duffwv/LayerFused-X301-Mods/blind-joint/base-sliding-tnut-spacers/spacers/img/spacers-side-org.jpeg

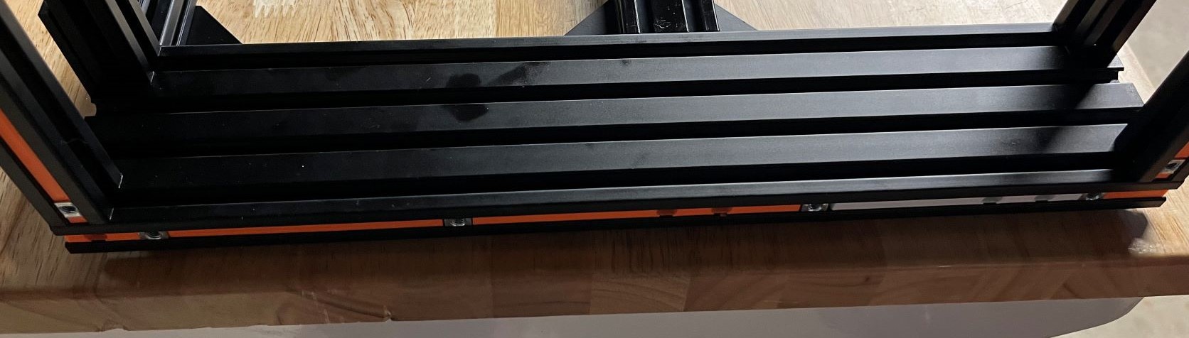
blind-joint/base-sliding-tnut-spacers/spacers/img/spacers-side-org.jpeg
