duffwv/LayerFused-X301-Mods/eva/diameter-17.7mm.png

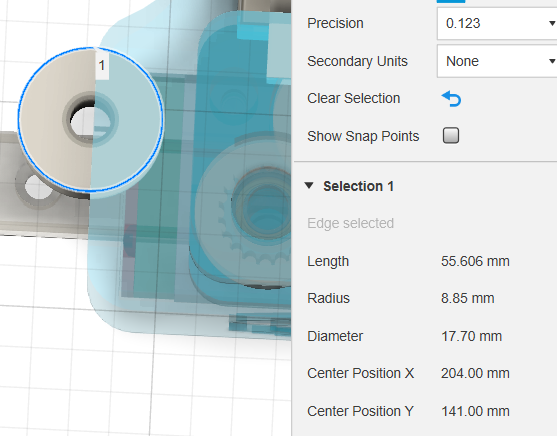
eva/diameter-17.7mm.png
