duffwv/LayerFused-X301-Mods/eva/from-right-front-12mm-drop.png

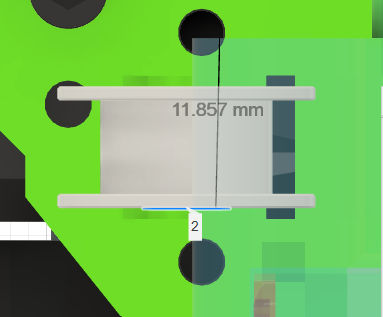
eva/from-right-front-12mm-drop.png
