duffwv/LayerFused-X301-Mods/MGN12C/XY Bracket Bottoms V2 Left.stl

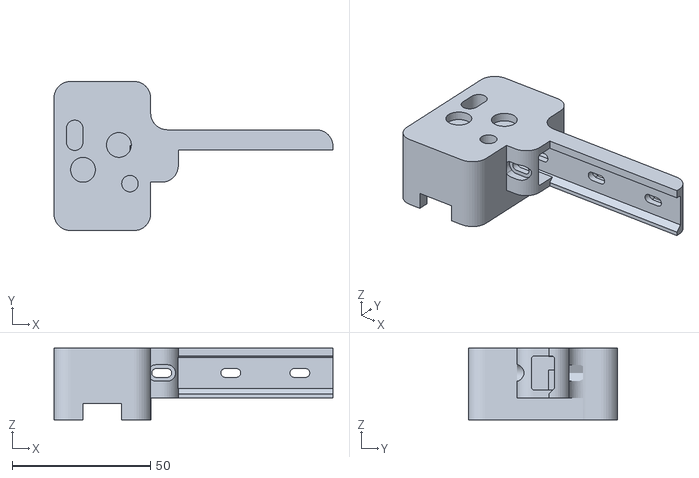
[picture p47: CAD file, 2023-02-08]
MGN12C/XY Bracket Bottoms V2 Left.stl
101.0 x 54.0 x 26.0
