duffwv/LayerFused-X301-Mods/sensorless-homing/y-homing-stops v2.stl

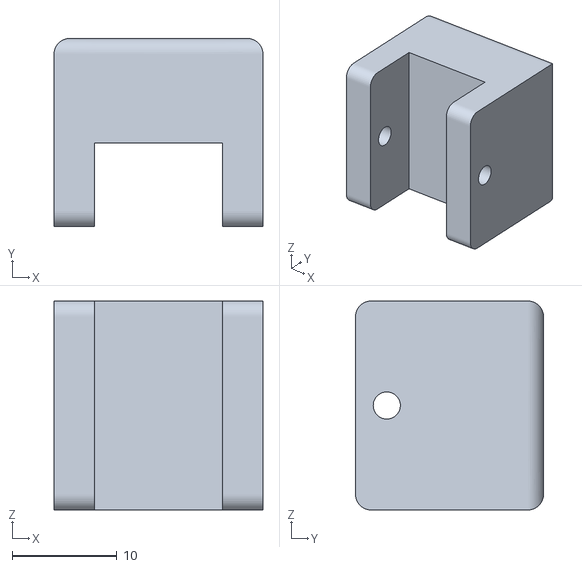
[picture p48: CAD file, 2023-02-08]
sensorless-homing/y-homing-stops v2.stl
20.0 x 18.0 x 20.0
