duffwv/LayerFused-X301-Mods/webcam-mount/stl/webcam-mount-plate-right.stl

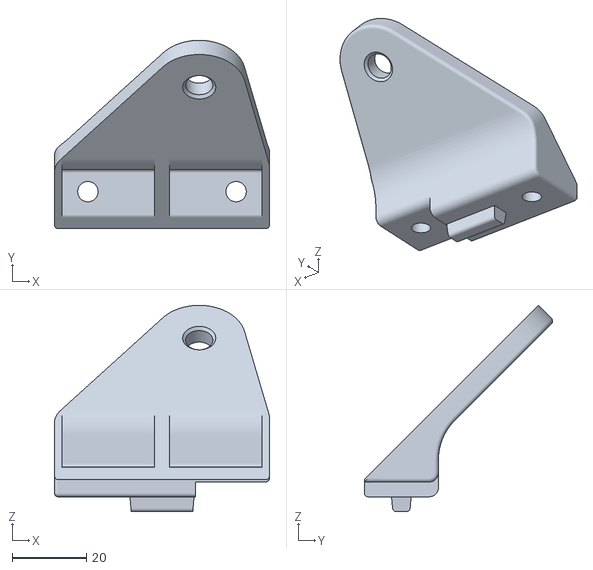
[picture p49: CAD file, 2023-02-08]
webcam-mount/stl/webcam-mount-plate-right.stl
58.0 x 50.8 x 55.7
