duffwv/LayerFused-X301-Mods/bed-leveling/bed-leveling-column-shim-1mm.stl

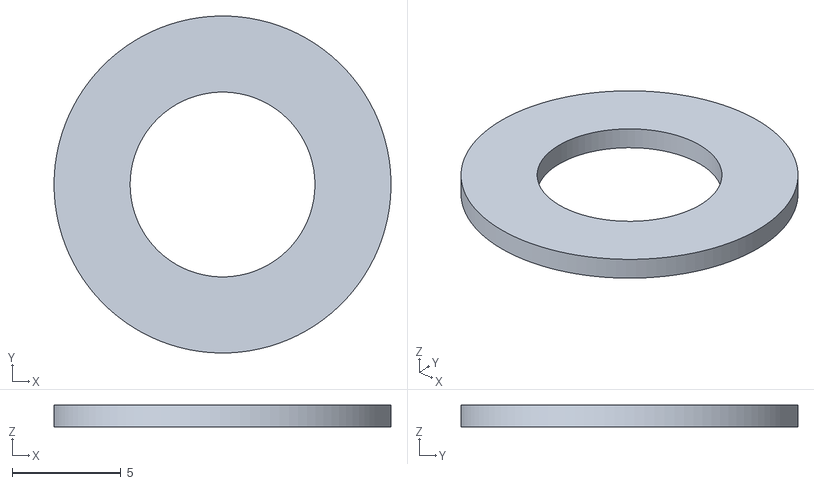
[picture p50: CAD file, 2023-02-08]
bed-leveling/bed-leveling-column-shim-1mm.stl
15.5 x 15.5 x 1.00
