duffwv/LayerFused-X301-Mods/blind-joint/base-sliding-tnut-spacers/spacers/STL/frontandback440mm/base-spacer-4mm.stl

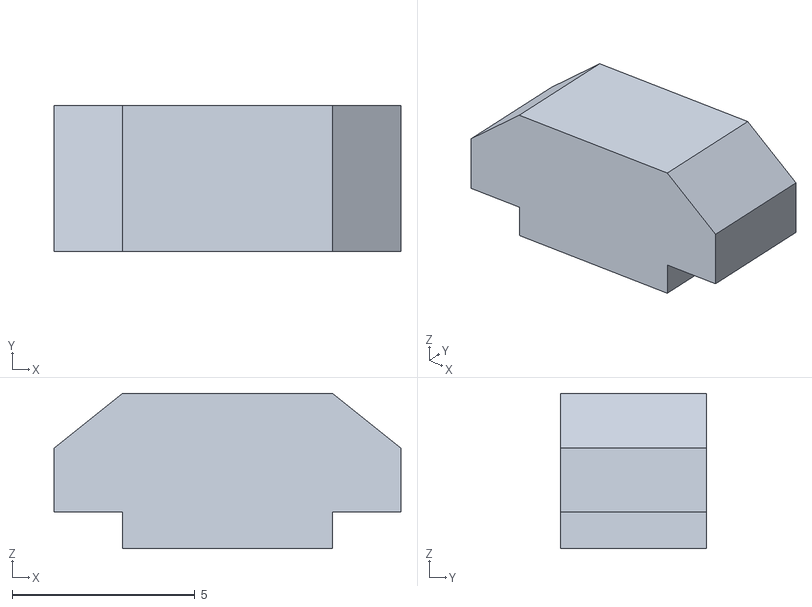
[picture p51: CAD file, 2023-02-08]
blind-joint/base-sliding-tnut-spacers/spacers/STL/frontandback440mm/base-spacer-4mm.stl
9.50 x 4.00 x 4.25
