duffwv/LayerFused-X301-Mods/blind-joint/base-sliding-tnut-spacers/spacers/STL/side400mm/base-spacer-119mm-slot29-slot49.stl

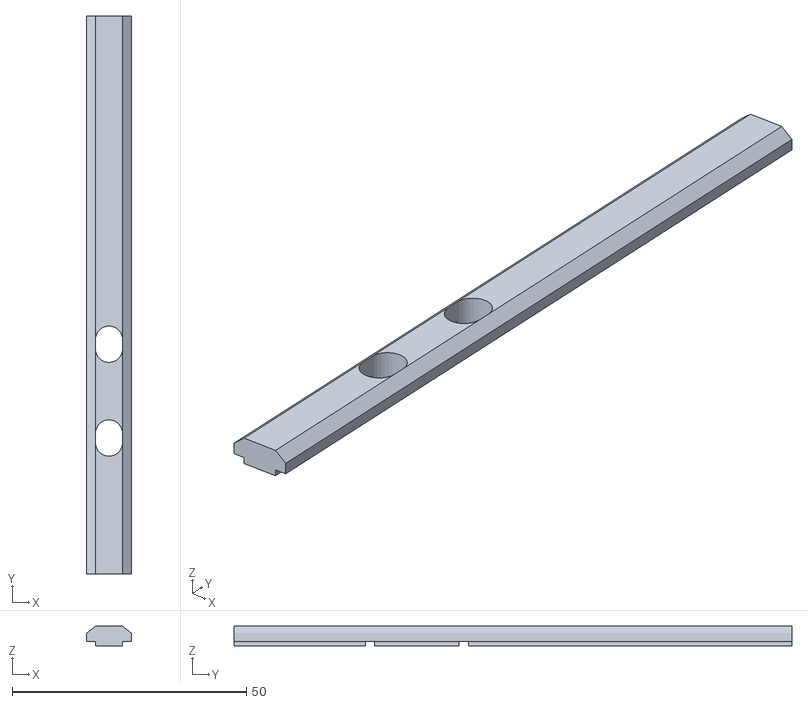
[picture p52: CAD file, 2023-02-08]
blind-joint/base-sliding-tnut-spacers/spacers/STL/side400mm/base-spacer-119mm-slot29-slot49.stl
9.50 x 119.0 x 4.25
