duffwv/LayerFused-X301-Mods/blind-joint/spacing_guides/extrusion-channel-center-punch-guides/blind-joint-drill-guide-10mm-and-3z v3.stl

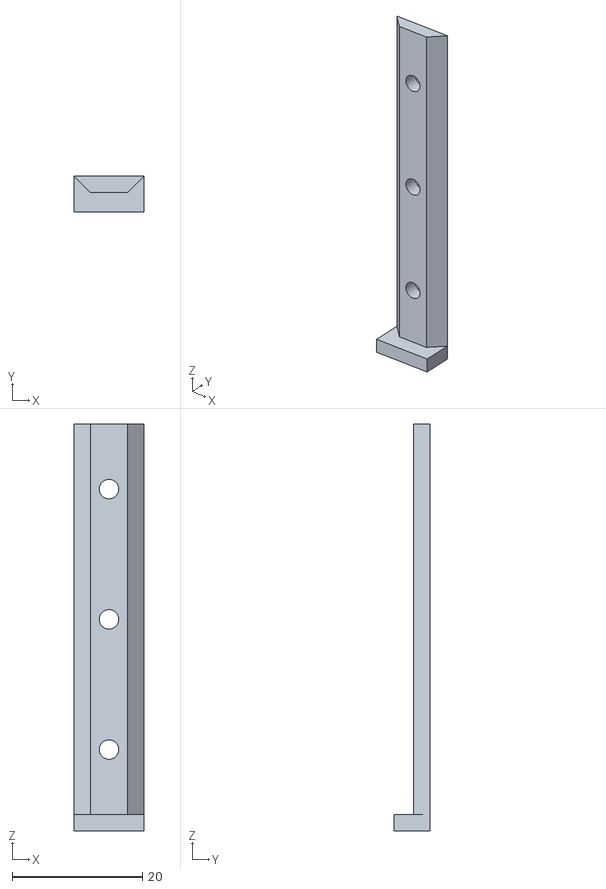
[picture p53: CAD file, 2023-02-08]
blind-joint/spacing_guides/extrusion-channel-center-punch-guides/blind-joint-drill-guide-10mm-and-3z v3.stl
10.8 x 5.50 x 62.5
