duffwv/LayerFused-X301-Mods/btt-tft35-spi-display-mount/TFT35 SPI Display Case - LayerFused X301.stl

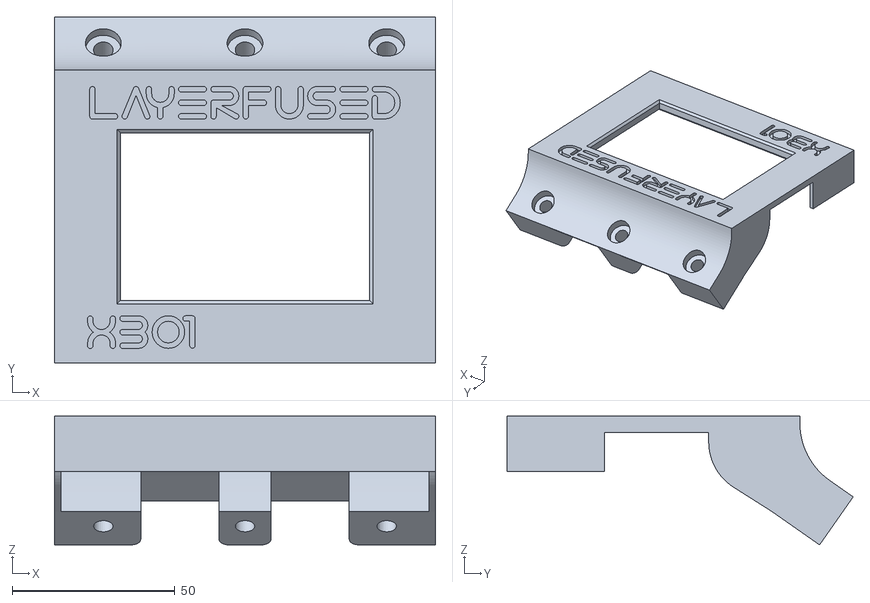
[picture p54: CAD file, 2023-02-08]
btt-tft35-spi-display-mount/TFT35 SPI Display Case - LayerFused X301.stl
117.0 x 106.4 x 39.6
