duffwv/LayerFused-X301-Mods/cover/1mm-pinch/cover-edges-straight-149.stl

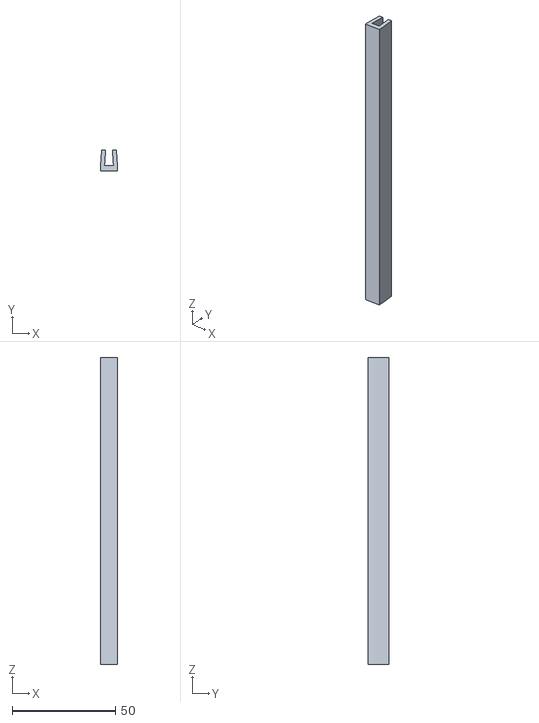
[picture p55: CAD file, 2023-02-08]
cover/1mm-pinch/cover-edges-straight-149.stl
8.25 x 10.0 x 149.0
