duffwv/LayerFused-X301-Mods/MGN12C/Z Carriage Bracket.stl

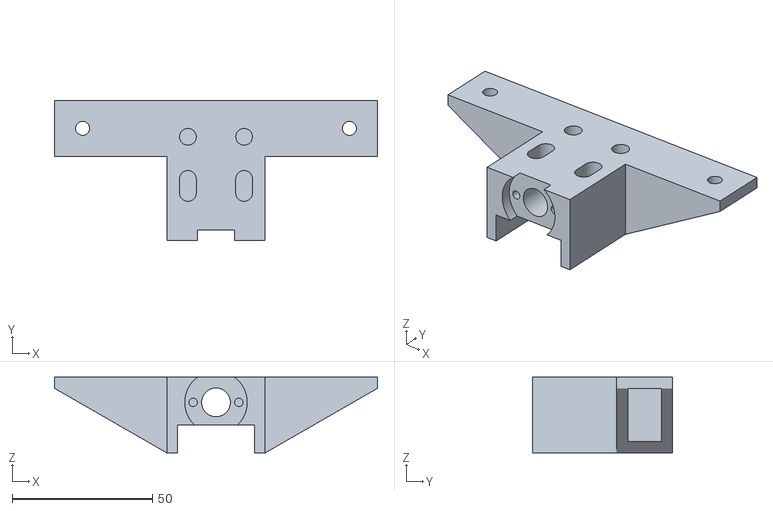
[picture p56: CAD file, 2023-02-08]
MGN12C/Z Carriage Bracket.stl
115.0 x 50.0 x 27.0
