duffwv/LayerFused-X301-Mods/webcam-mount/stl/webcam-mount-flush.stl

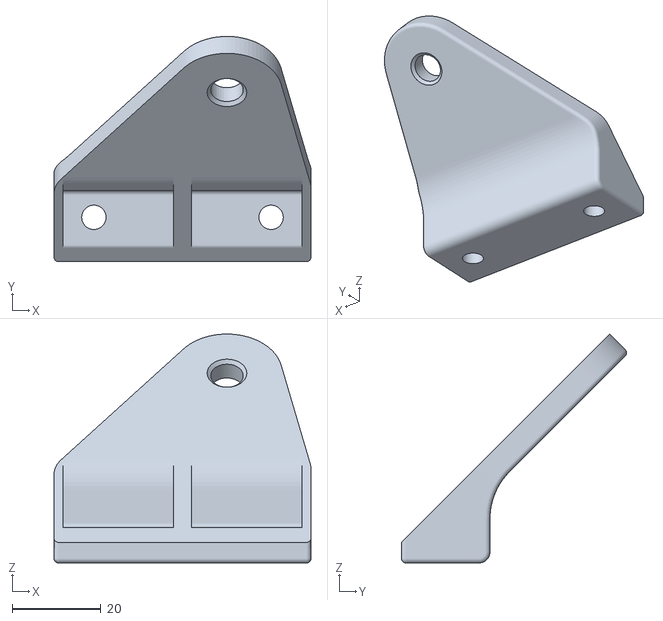
[picture p57: CAD file, 2023-02-08]
webcam-mount/stl/webcam-mount-flush.stl
58.0 x 50.8 x 51.7
