duffwv/LayerFused-X301-Mods/blind-joint/base-sliding-tnut-spacers/spacers/STL/frontandback440mm/base-spacer-front-back-104.stl

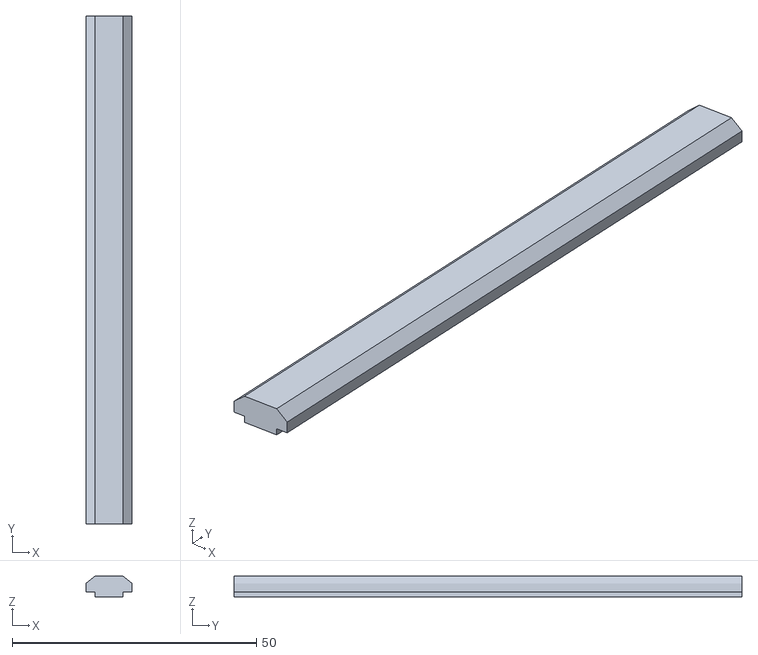
[picture p58: CAD file, 2023-02-08]
blind-joint/base-sliding-tnut-spacers/spacers/STL/frontandback440mm/base-spacer-front-back-104.stl
9.50 x 104.0 x 4.25
