duffwv/LayerFused-X301-Mods/blind-joint/base-sliding-tnut-spacers/spacers/STL/side400mm/base-spacer-94mm.stl

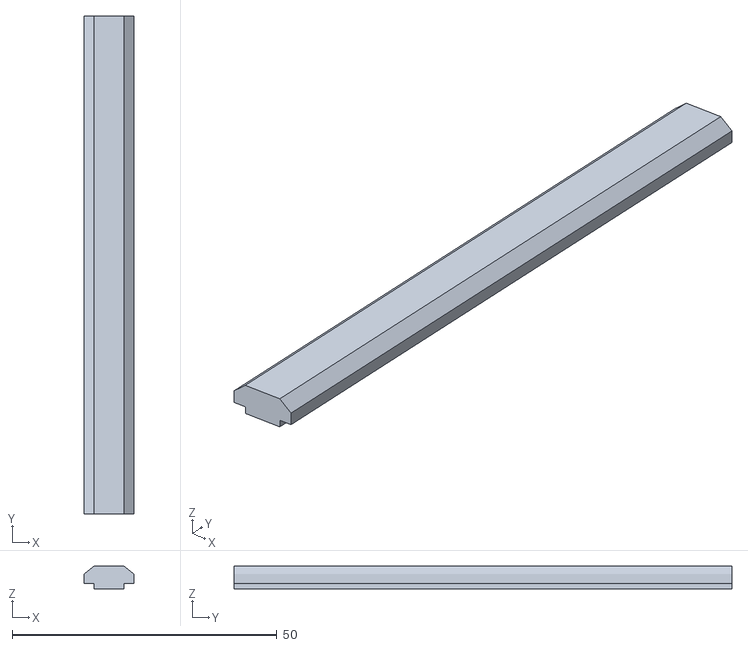
[picture p59: CAD file, 2023-02-08]
blind-joint/base-sliding-tnut-spacers/spacers/STL/side400mm/base-spacer-94mm.stl
9.50 x 94.0 x 4.25
