duffwv/LayerFused-X301-Mods/cover/1mm-pinch/cover-edges-corner-10mm.stl

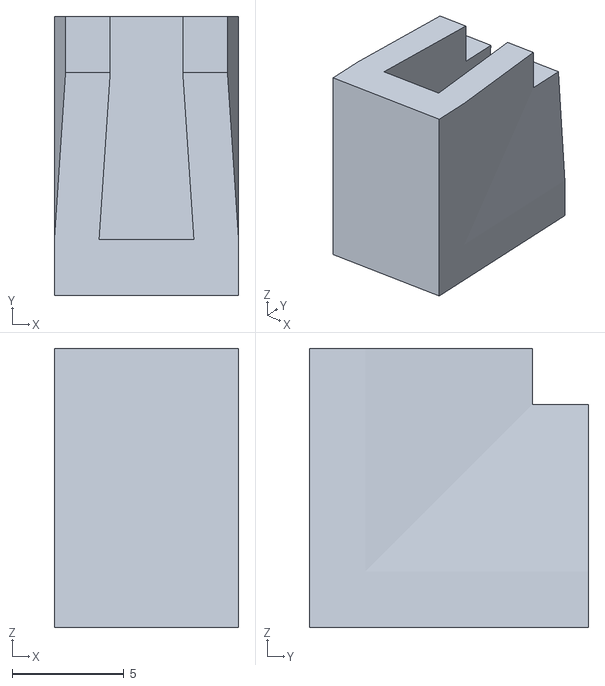
[picture p60: CAD file, 2023-02-08]
cover/1mm-pinch/cover-edges-corner-10mm.stl
8.25 x 12.5 x 12.5
