duffwv/LayerFused-X301-Mods/electronics-enclosure/board-mounts/mb8.stl

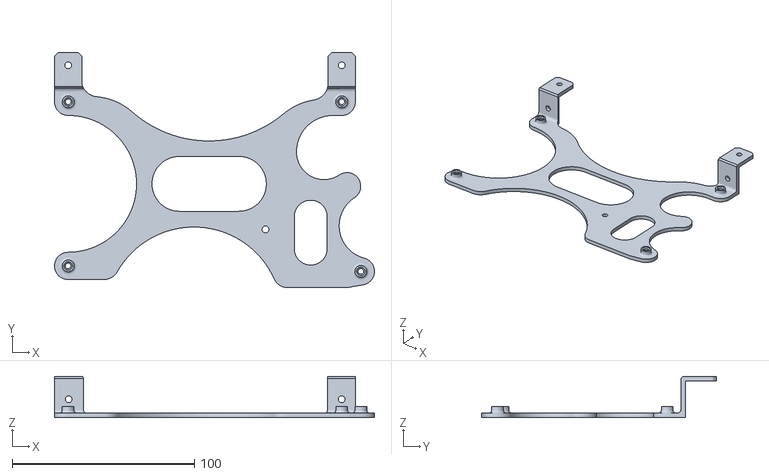
[picture p61: CAD file, 2023-02-08]
electronics-enclosure/board-mounts/mb8.stl
175.5 x 128.8 x 22.5
