duffwv/LayerFused-X301-Mods/bed-leveling/bed-leveling-column-shim-2mm.stl

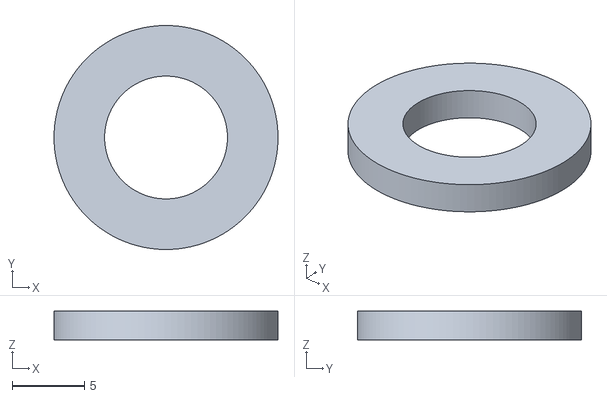
[picture p63: CAD file, 2023-02-08]
bed-leveling/bed-leveling-column-shim-2mm.stl
15.5 x 15.5 x 2.00
