duffwv/LayerFused-X301-Mods/cover/1mm-pinch/cover-edges-corner-47.5mm-27.5mm.stl

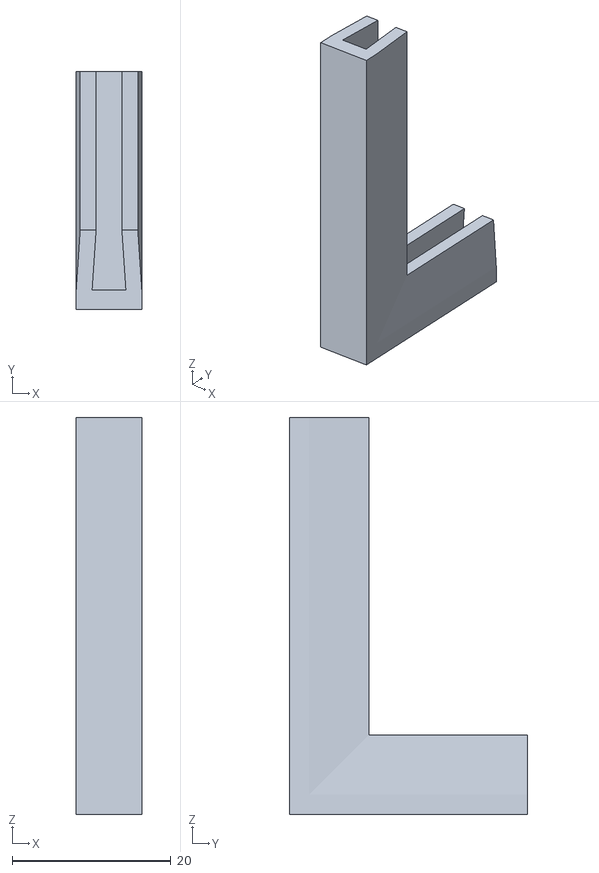
[picture p64: CAD file, 2023-02-08]
cover/1mm-pinch/cover-edges-corner-47.5mm-27.5mm.stl
8.25 x 30.0 x 50.0
