duffwv/LayerFused-X301-Mods/blind-joint/base-sliding-tnut-spacers/spacers/STL/side400mm/base-spacer-24mm.stl

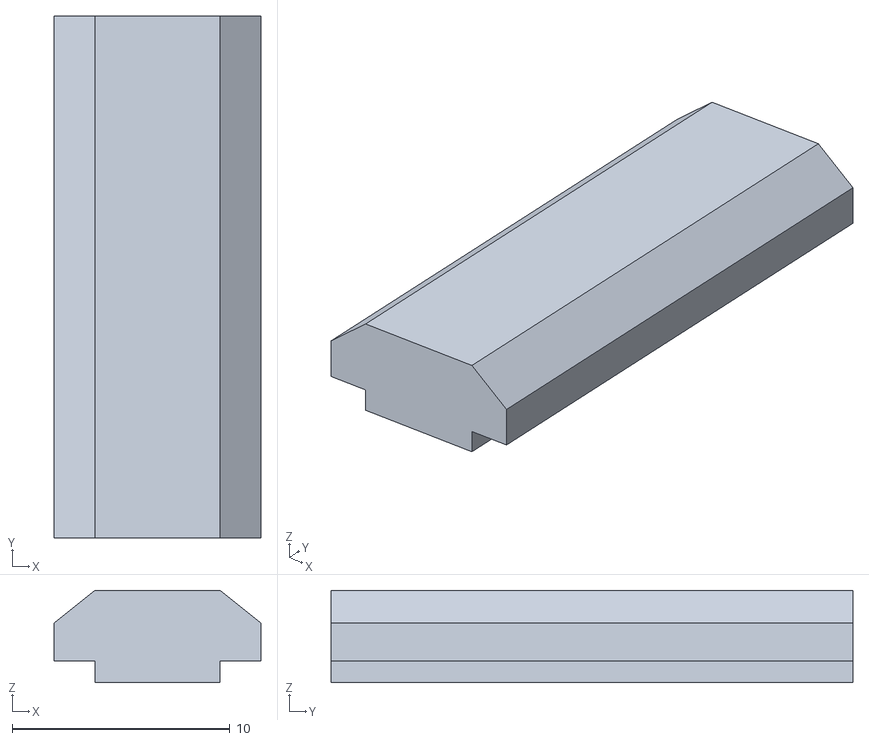
[picture p66: CAD file, 2023-02-08]
blind-joint/base-sliding-tnut-spacers/spacers/STL/side400mm/base-spacer-24mm.stl
9.50 x 24.0 x 4.25
