duffwv/LayerFused-X301-Mods/cover/1mm-pinch/cover-edges-straight-89.stl

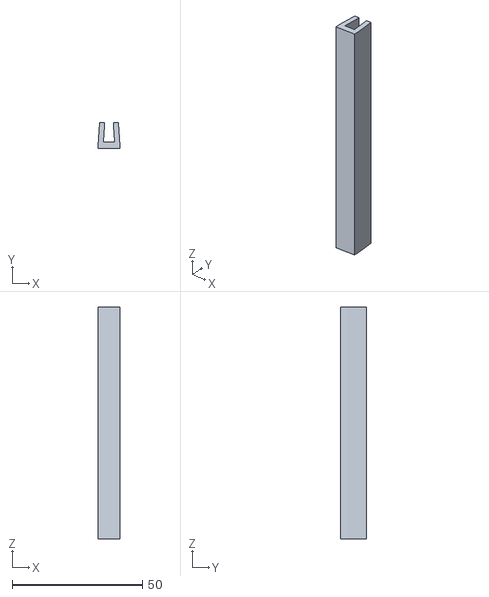
[picture p67: CAD file, 2023-02-08]
cover/1mm-pinch/cover-edges-straight-89.stl
8.25 x 10.0 x 89.0
