duffwv/LayerFused-X301-Mods/cover/1mm-pinch/cover-edges-testfit.stl

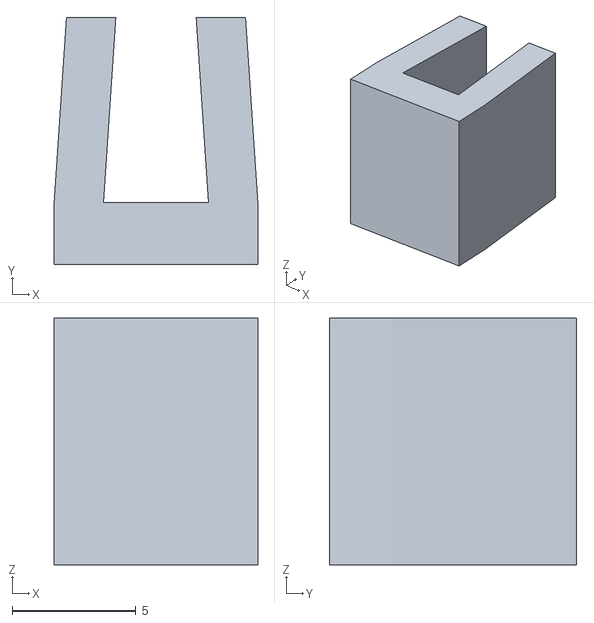
[picture p68: CAD file, 2023-02-08]
cover/1mm-pinch/cover-edges-testfit.stl
8.25 x 10.0 x 10.0
