duffwv/LayerFused-X301-Mods/cover/1mm-pinch/cover-edges-stepper.stl

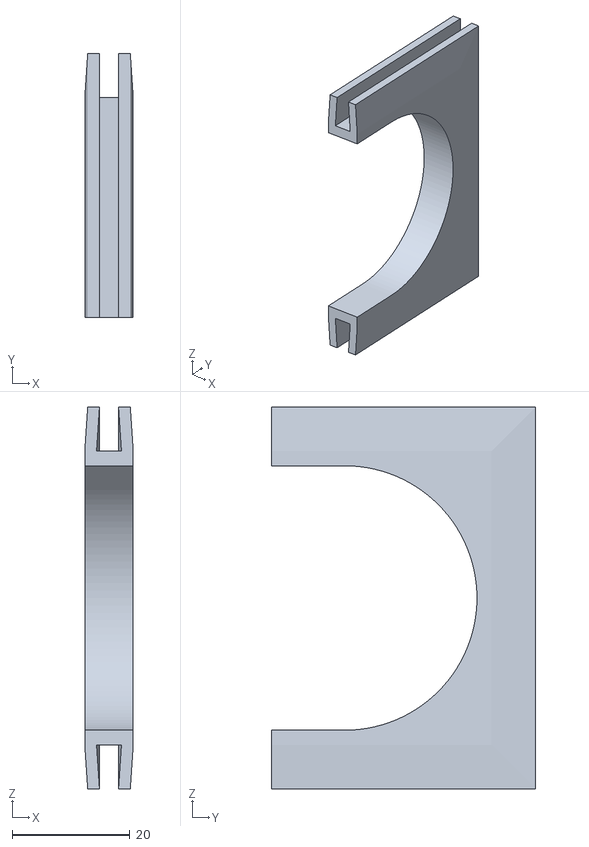
[picture p69: CAD file, 2023-02-08]
cover/1mm-pinch/cover-edges-stepper.stl
8.25 x 45.0 x 65.0
